aclandmark/PCB_111000_V3/1_Arduino Projects/5_Interrupts/4_Rx_interrupts/4B_Rx_interrupt/4B_Rx_interrupt.ino

/*
 A crude attempt to implement a new line function without also
 resetting the cursor to the start of the line 
 */

volatile char sym_counter;

#include "4B_Rx_interrupt_header.h"


//Type main here


ISR(USART_RX_vect){
Char_from_PC_Basic();
newline_Basic();
for (int m = 0; m <= sym_counter; m++)String_to_PC_Basic(" ");}




/*******************************************************************/
