aclandmark/PCB_111000_V3/4_Resources_nano_projects/PC_comms/Basic_Rx_Tx_Arduino.c

void I2C_Tx(char, char, char*);

void send_byte_with_Ack(char);
void send_byte_with_Nack(char);
char receive_byte_with_Ack(void);
char receive_byte_with_Nack(void);
void I2C_Tx_initiate_mode(char);




/**********************************************************************************************************************************************************************************/
char isCharavailable_A (int m){int n = 0;								//Version of isCharavailable_Basic() that uses the Arduino library
while (!(Serial.available())){n++;	wdr();			
if (n>8000) {m--;n = 0;}if (m == 0)return 0;}	
return 1;}	



/**********************************************************************************************************************************************************************************/
char waitforkeypress_A (void){											//Version of waitforkeypress_Basic() that uses the Arduino library
while (!(Serial.available()))wdr();	
return Serial.read(); }



/**********************************************************************************************************************************************************************************/
char wait_for_return_key_A(void){                  						//Returns key presses one at a time
char keypress,temp;
while(1){																//Remain in while loop until a character is received
if (isCharavailable_A(8)){												//Pauses but returns 1 immediately that a character is received
keypress = Serial.read();												//Skip if no character has been received 
break;}}																//Exit while loop when character has been read
if((keypress == '\r') || (keypress == '\n')){							//Detect \r\n, \r or \n and converts to \r
if (isCharavailable_A(1)){temp = Serial.read();}
keypress = '\r';}
return keypress;}



/**********************************************************************************************************************************************************************************/
void newline_A(void){Serial.write ("\r\n");}




/**********************************************************************************************************************************************************************************/
char decimal_digit_A (char data){											//Returns 1 if data is a character of 0 to 9 inclusive
if (((data > '9') || (data < '0')) )return 0;							//Otherwise return zero
else return 1;}



/*********************************************************************/
char hex_digit (char data){
switch(data){
case '0': case '1': case '2': case '3': case '4': case '5': case '6':
case '7': case '8': case '9': case 'A': case 'B': case 'C': case 'D':
case 'E': case 'F': return 1; break;
default: return 0; break;}}



/**********************************************************************************************************************************************************************************/
void Check_num_for_to_big_or_small(float num)											//Exits if the result of floating point arithmetic exceeds permitted limits 
{unsigned long * long_ptr;
long_ptr = (unsigned long *)&num;														//Enables floating point number to be read as a 32 bit integer 
if (*long_ptr == 0x7F800000){Serial.write("+ve Num too large\r\n"); eeprom_write_byte((uint8_t*)0x3FA, 0);SW_reset;}
if (*long_ptr == 0xFF800000){Serial.write("-ve Num too large\r\n"); eeprom_write_byte((uint8_t*)0x3FA, 0); SW_reset;}
if (*long_ptr == 0X0){Serial.write("+ve Num too small\r\n"); eeprom_write_byte((uint8_t*)0x3FA, 0); SW_reset;}
if (*long_ptr == 0X80000000){Serial.write("-ve Num too small\r\n"); eeprom_write_byte((uint8_t*)0x3FA, 0); SW_reset;}}



/**********************************************************************************************************************************************************************************/
void Cal_UNO_pcb_A_Arduino(void)
{unsigned char OSCCAL_mini_OS;
int error_mag;
char cal_string[12];

User_prompt_A;
I2C_Tx_initiate_mode('R');
Serial.write("\r\nPCB_A (mini_OS) device calibrating");
waiting_for_I2C_master;  
OSCCAL_mini_OS = receive_byte_with_Ack();
error_mag = receive_byte_with_Ack() << 8;
error_mag += receive_byte_with_Nack();
clear_I2C_interrupt;
Serial.write("\r\nOSCCAL user value   "); 
itoa(OSCCAL_mini_OS, cal_string, 10);Serial.write(cal_string);

Serial.write("\r\ncalibration error  "); 
itoa(error_mag, cal_string, 10);Serial.write(cal_string);
if (error_mag < 750) Serial.write("  OK\r\n");}


/**********************************************************************************************************************************************************************************/
void Read_Hello_world_string_A(void){
char receive_byte;

I2C_Tx_initiate_mode('H');
waiting_for_I2C_master;									//Initiate comuninations:master to send string
do{receive_byte = receive_byte_with_Ack();				//print out string as characters are received
if(receive_byte)Serial.write(receive_byte);}
while(receive_byte);									//Detect '\0' character used to terminate a string
receive_byte_with_Nack();								//Receve a second null char at the end of the string
clear_I2C_interrupt;}									//Complete transaction



/************************************************************************/
void I2C_Rx_get_version_A(char str_type){			//NEEDED
char num_bytes=1; char mode='P';
char s[2];

s[0]= str_type; s[1]=0;
I2C_Tx(num_bytes,mode, s);
waiting_for_I2C_master;
num_bytes = (receive_byte_with_Ack() - '0') * 10;
num_bytes += (receive_byte_with_Ack() - '0');
for (int m = 0; m < num_bytes; m++){
if (m ==(num_bytes-1)){Serial.write(receive_byte_with_Nack());}
else {Serial.write(receive_byte_with_Ack());}}
TWCR = (1 << TWINT);}
